nostradomus/LabTools_Analogue-input-slider-panel/images/Slider-panel-pcb-m.png

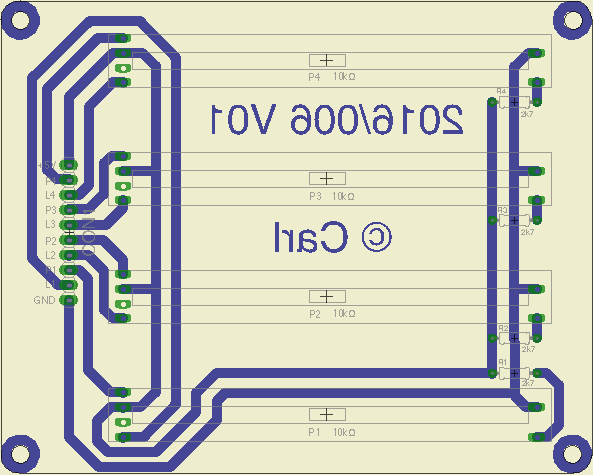
images/Slider-panel-pcb-m.png
