nostradomus/LabTools_Analogue-input-slider-panel/images/Slider-panel-pcbview-s.png

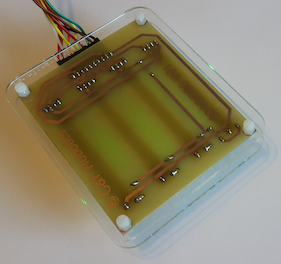
images/Slider-panel-pcbview-s.png
